MilanBowz/Project_Ontwerpen_KlokWave/Tests/Buttons/Buttons.image01.jpg

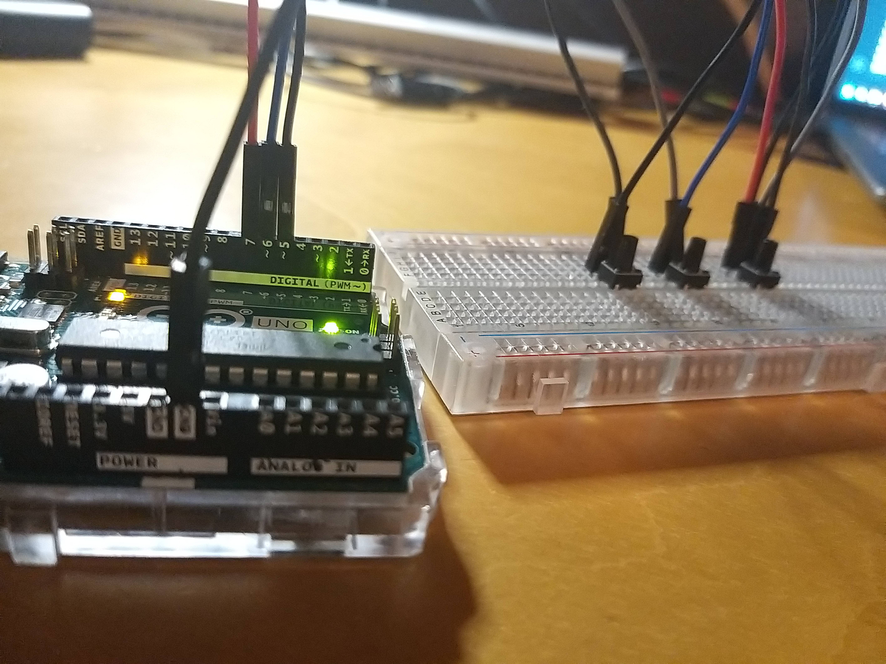
Tests/Buttons/Buttons.image01.jpg
