MilanBowz/Project_Ontwerpen_KlokWave/Tests/Schuifregister/74HC595N.image02.jpg

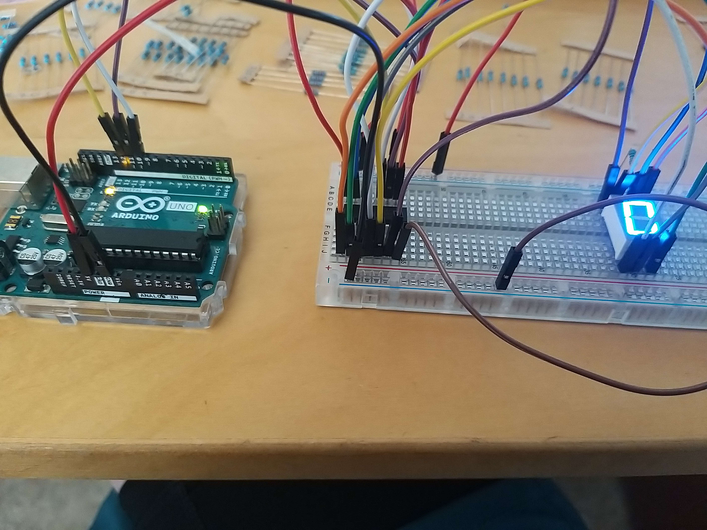
Tests/Schuifregister/74HC595N.image02.jpg
